b1u3-22/LPED/hardware/lped_dock/single_dock/3d_models/step/lped_dock_pcb.step

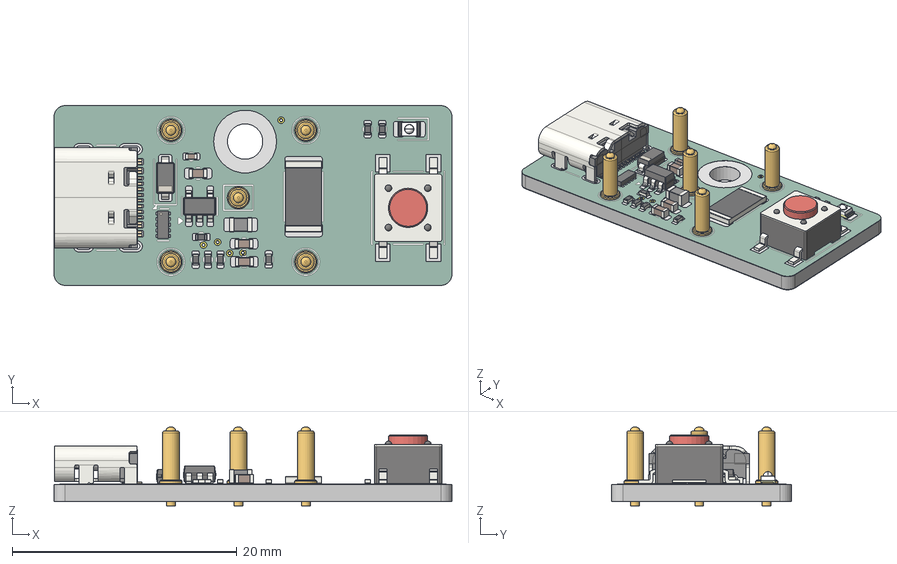
[picture p15: CAD file, 2025-06-25]
hardware/lped_dock/single_dock/3d_models/step/lped_dock_pcb.step
35.4 x 16.0 x 7.00 mm
R_0402_1005Metric x 7
USB_C_Receptacle_GCT_USB4105-xx-A_16P_TopMnt_Horizontal
L_0805_2012Metric
pogo_pin-7mm x 5
C_0603_1608Metric x 3
APTD2012LSURCK
R_2512_6332Metric
SW_SPST_PTS645
D_SOD-123
USON-10_2.5x1.0mm_P0.5mm
SOT-23-5
C_0402_1005Metric
lped_dock_copper
lped_dock_pad
lped_dock_via
lped_dock_silkscreen
lped_dock_soldermask
lped_dock_PCB
