b1u3-22/LPED/hardware/lped/3d_models/step/die_20_insert.step

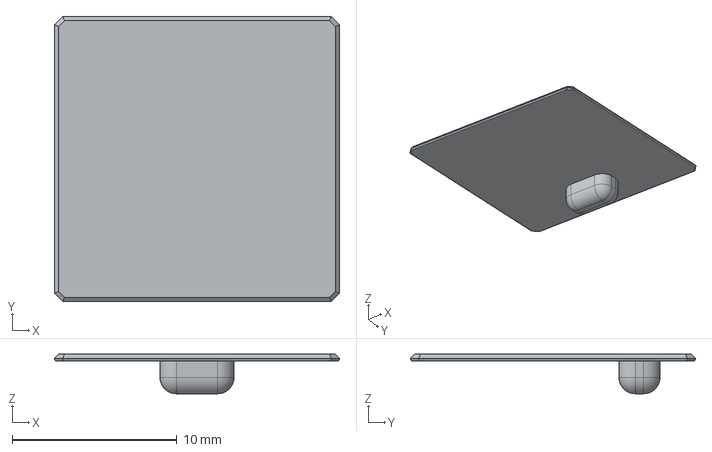
[picture p16: CAD file, 2025-06-25]
hardware/lped/3d_models/step/die_20_insert.step
17.3 x 17.3 x 2.40 mm
