b1u3-22/LPED/hardware/lped_dock/single_dock/3d_models/step/top_body.step

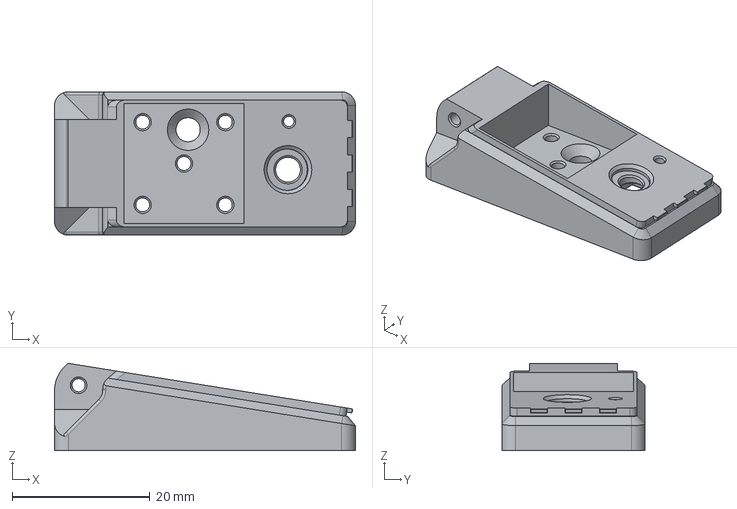
[picture p17: CAD file, 2025-06-25]
hardware/lped_dock/single_dock/3d_models/step/top_body.step
43.7 x 20.8 x 12.7 mm
