b1u3-22/LPED/hardware/3d_models/FA-128_EPS.step

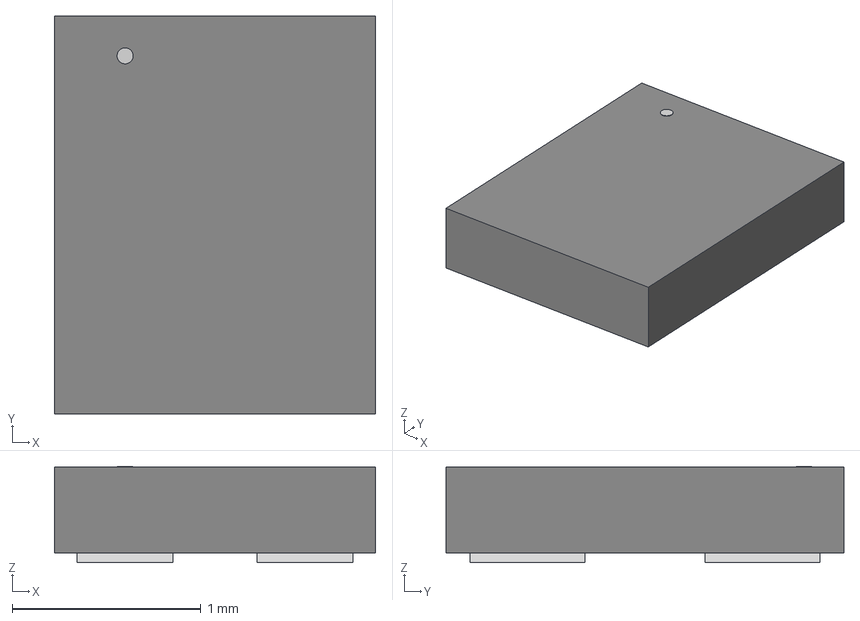
[picture p18: CAD file, 2025-06-25]
hardware/3d_models/FA-128_EPS.step
1.70 x 2.11 x 0.511 mm
