b1u3-22/LPED/hardware/lped/3d_models/step/lped_pcb.step

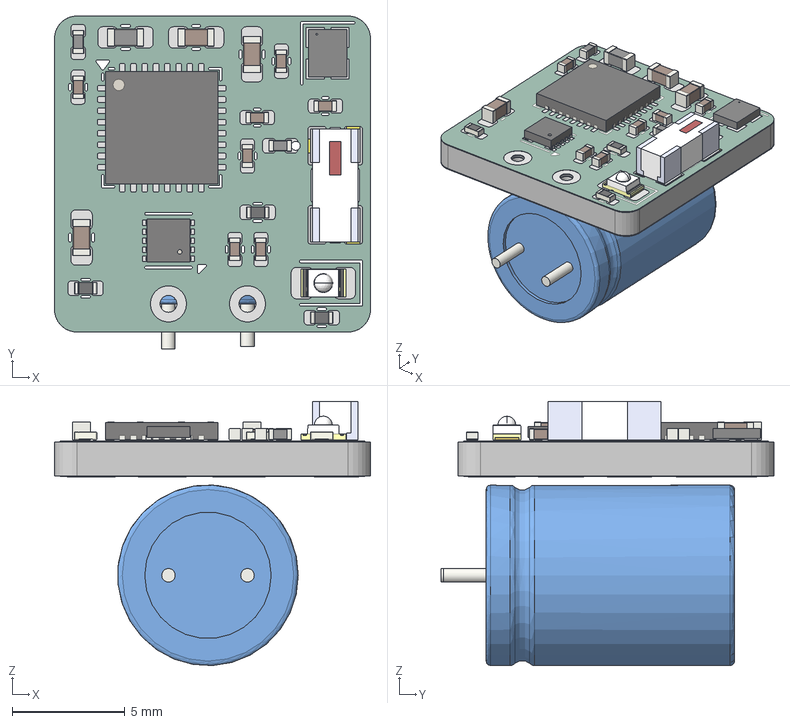
[picture p19: CAD file, 2025-06-25]
hardware/lped/3d_models/step/lped_pcb.step
14.0 x 14.8 x 11.7 mm
C_0402_1005Metric x 7
C_Radial_D8.0mm_H11.5mm_P3.50mm
fxls8974cf
C_0603_1608Metric x 3
R_0402_1005Metric x 3
APTD2012LSURCK
FA-128_EPS
L_0402_1005Metric x 2
L_0603_1608Metric
QFN-32-1EP_5x5mm_P0.5mm_EP3.45x3.45mm
2450AT42E010BE
lped_copper
lped_pad
lped_via
lped_silkscreen
lped_soldermask
lped_PCB
