b1u3-22/LPED/hardware/lped_dock/single_dock/3d_models/step/lid.step

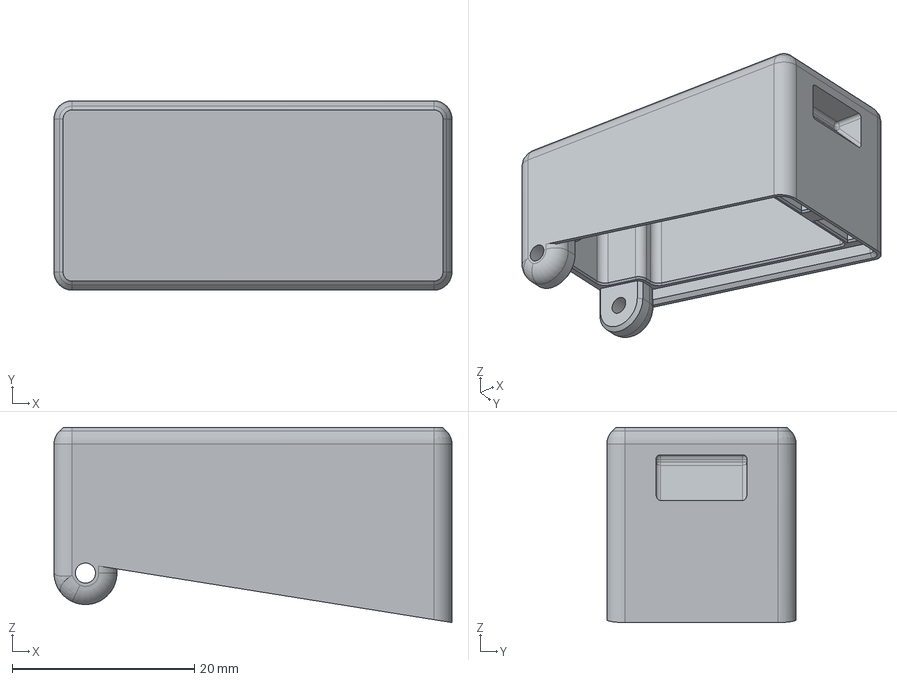
[picture p20: CAD file, 2025-06-25]
hardware/lped_dock/single_dock/3d_models/step/lid.step
43.7 x 20.8 x 21.4 mm
