b1u3-22/LPED/hardware/3d_models/pogo_pin-3mm.step

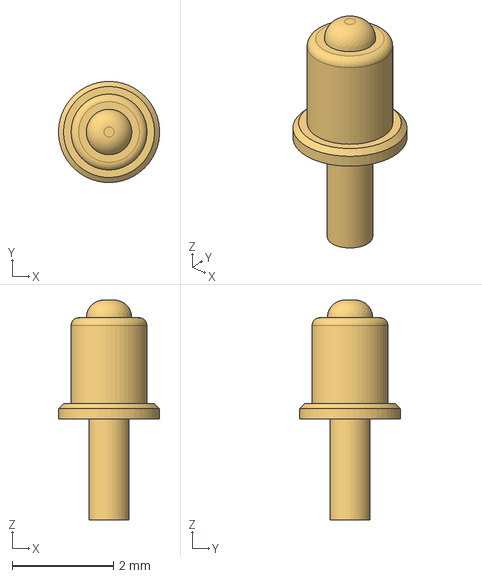
[picture p21: CAD file, 2025-06-25]
hardware/3d_models/pogo_pin-3mm.step
2.00 x 2.00 x 4.35 mm
