b1u3-22/LPED/hardware/lped/3d_models/step/cap.step

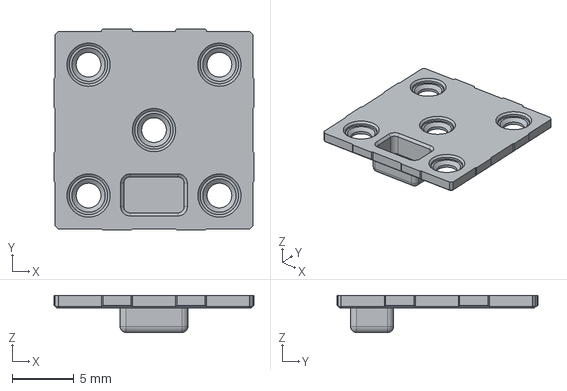
[picture p22: CAD file, 2025-06-25]
hardware/lped/3d_models/step/cap.step
16.2 x 16.3 x 3.00 mm
