b1u3-22/LPED/hardware/3d_models/2450AT42E010BE.step

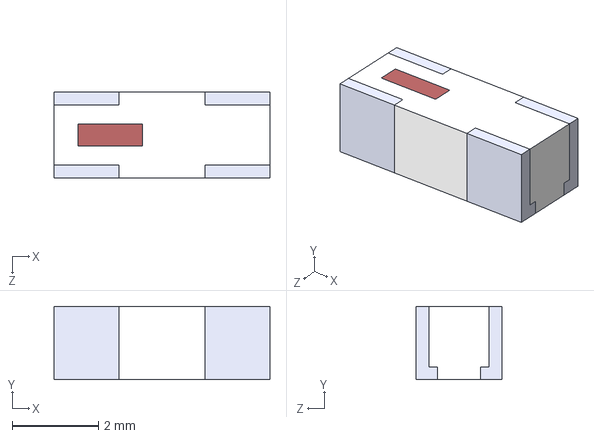
[picture p23: CAD file, 2025-06-25]
hardware/3d_models/2450AT42E010BE.step
5.00 x 1.70 x 2.00 mm
