b1u3-22/LPED/hardware/3d_models/APTD2012LSURCK.stp

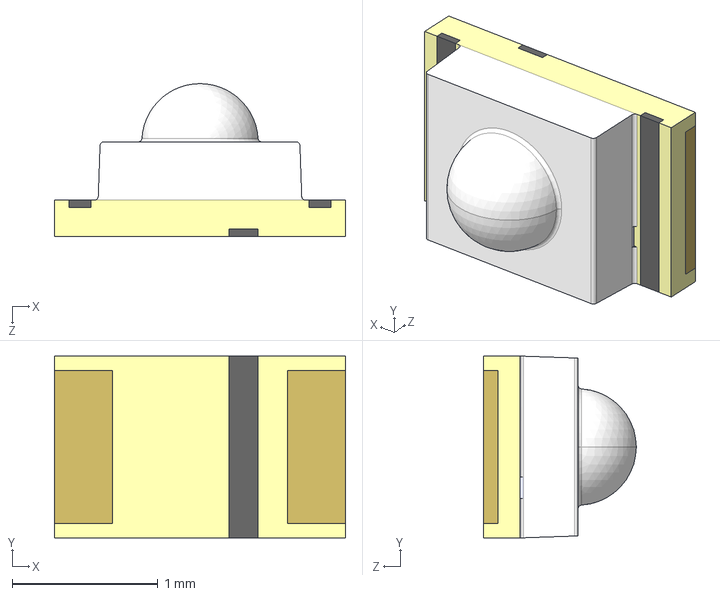
[picture p24: CAD file, 2025-06-25]
hardware/3d_models/APTD2012LSURCK.stp
2.00 x 1.25 x 1.05 mm
